Wnt2Fly/Peanut2Shield/src/hid_peripheral.cpp

#include "hid_peripheral.h"
#include "config.h"
#include "devlog.h"
#include <NimBLEDevice.h>
#include <Preferences.h>
#include <Arduino.h>
#if CFG_SHIELD_DEBUG
#include <esp_system.h>
#endif

static Preferences sShieldPrefs;

#if CFG_SHIELD_DEBUG
static unsigned long sShieldConnectAt       = 0;
static unsigned long sShieldFastParamsAt    = 0;
static unsigned long sShieldLastHeartbeatAt = 0;
static unsigned long sShieldLastDropAt      = 0;
static uint16_t      sShieldLastConnItvl    = 0;
static uint16_t      sShieldLastSupervision = 0;
#endif

static bool isTivoBondAddr(const NimBLEAddress& addr, NimBLEAddress tivoAddr, bool hasTivo) {
  if (!hasTivo) return false;
  return addr == tivoAddr;
}

// HID Report Descriptor
//   Report ID 1 — standard keyboard  (8 bytes: modifier, reserved, key[6])
//   Report ID 2 — consumer control   (2 bytes: usage LE16)
static const uint8_t kReportDesc[] = {
  // ---- Keyboard (Report ID 1) ----
  0x05, 0x01,         // Usage Page (Generic Desktop)
  0x09, 0x06,         // Usage (Keyboard)
  0xA1, 0x01,         // Collection (Application)
    0x85, 0x01,       //   Report ID (1)
    // Modifier byte
    0x05, 0x07,       //   Usage Page (Key Codes)
    0x19, 0xE0,       //   Usage Minimum (L-Ctrl)
    0x29, 0xE7,       //   Usage Maximum (R-GUI)
    0x15, 0x00,       //   Logical Minimum (0)
    0x25, 0x01,       //   Logical Maximum (1)
    0x75, 0x01,       //   Report Size (1 bit)
    0x95, 0x08,       //   Report Count (8)
    0x81, 0x02,       //   Input (Data, Variable, Absolute)
    // Reserved byte
    0x75, 0x08,       //   Report Size (8 bits)
    0x95, 0x01,       //   Report Count (1)
    0x81, 0x01,       //   Input (Constant)
    // Key array
    0x75, 0x08,       //   Report Size (8 bits)
    0x95, 0x06,       //   Report Count (6)
    0x15, 0x00,       //   Logical Minimum (0)
    0x26, 0xFF, 0x00, //   Logical Maximum (255)
    0x19, 0x00,       //   Usage Minimum (0)
    0x29, 0xFF,       //   Usage Maximum (255)
    0x81, 0x00,       //   Input (Data, Array)
  0xC0,               // End Collection

  // ---- Consumer Control (Report ID 2) ----
  0x05, 0x0C,         // Usage Page (Consumer)
  0x09, 0x01,         // Usage (Consumer Control)
  0xA1, 0x01,         // Collection (Application)
    0x85, 0x02,       //   Report ID (2)
    0x19, 0x00,       //   Usage Minimum (0)
    0x2A, 0xFF, 0x03, //   Usage Maximum (1023)
    0x15, 0x00,       //   Logical Minimum (0)
    0x26, 0xFF, 0x03, //   Logical Maximum (1023)
    0x75, 0x10,       //   Report Size (16 bits)
    0x95, 0x01,       //   Report Count (1)
    0x81, 0x00,       //   Input (Data, Array)
  0xC0,               // End Collection
};

static NimBLEServer*         pServer              = nullptr;
static NimBLECharacteristic* pKbReport            = nullptr;
static NimBLECharacteristic* pCsReport            = nullptr;
static bool                  sShieldConn          = false;
static NimBLEAddress         sShieldAddr;
static bool                  sHasShieldAddr       = false;
static uint16_t              sShieldConnHandle    = BLE_HS_CONN_HANDLE_NONE;
// true between onConnect and the first CCCD write — Shield is doing service discovery
static bool                  sShieldNegotiating   = false;
static bool                  sAdvPausedForTivo      = false;
static bool                  sTivoLinkActive        = false;
static bool                  sAdvSlowForTivo        = false;

#if CFG_SHIELD_DEBUG
static void shieldDebugLogAdv(const char* tag);
static void shieldDebugLogConnDesc(const char* tag, ble_gap_conn_desc* desc);
#endif

// Start (or restart) advertising with intervals appropriate for dual-role state.
static void startAdvertisingAppropriate() {
  NimBLEAdvertising* pAdv = NimBLEDevice::getAdvertising();
  if (!pAdv) return;

  const bool slow = sTivoLinkActive && !sShieldConn;
  if (pAdv->isAdvertising()) pAdv->stop();
  if (slow) {
    pAdv->setMinInterval(CFG_ADV_SLOW_MIN_INTERVAL);
    pAdv->setMaxInterval(CFG_ADV_SLOW_MAX_INTERVAL);
  } else {
    pAdv->setMinInterval(CFG_ADV_MIN_INTERVAL);
    pAdv->setMaxInterval(CFG_ADV_MAX_INTERVAL);
  }
  pAdv->start();
  sAdvPausedForTivo = false;
  sAdvSlowForTivo   = slow;
  if (slow) {
    DEV_LOGLN("[HID] Advertising (slow) — protecting TiVo central link.");
  } else {
    DEV_LOGLN("[HID] Advertising (fast).");
  }
}

// Log every CCCD write so we can confirm the Shield is enabling notifications
class ReportCallbacks : public NimBLECharacteristicCallbacks {
  void onSubscribe(NimBLECharacteristic* pChar,
                   ble_gap_conn_desc*    desc,
                   uint16_t             subValue) override {
    DEV_LOGF("[HID] CCCD write — subValue=0x%04X "
                  "(1=notify enabled, 0=disabled)\r\n", subValue);
    // First CCCD write means Android has finished service discovery
    if (subValue & 0x0001) {
      if (sShieldNegotiating) {
        sShieldNegotiating = false;
        hidPersistShieldBond();
      }
    }
  }
};
static ReportCallbacks sReportCbs;

class PeriphCallbacks : public NimBLEServerCallbacks {
  void onConnect(NimBLEServer* s, ble_gap_conn_desc* desc) override {
    sShieldConn         = true;
    sShieldNegotiating  = true;   // waiting for Android to write CCCDs
    sShieldAddr         = NimBLEAddress(desc->peer_id_addr);
    sHasShieldAddr      = true;
    sShieldConnHandle   = desc->conn_handle;
#if CFG_SHIELD_DEBUG
    sShieldConnectAt = millis();
#endif
    DEV_LOGF("[HID] Shield connected: %s handle=%u\r\n",
                  sShieldAddr.toString().c_str(), sShieldConnHandle);
#if CFG_SHIELD_DEBUG
    shieldDebugLogConnDesc("Shield connect", desc);
#endif
    NimBLEDevice::getAdvertising()->stop();
  }

  void onDisconnect(NimBLEServer* s, ble_gap_conn_desc* desc) override {
    unsigned long upMs = 0;
#if CFG_SHIELD_DEBUG
    if (sShieldConnectAt) upMs = millis() - sShieldConnectAt;
    unsigned long sinceFast = sShieldFastParamsAt ? (millis() - sShieldFastParamsAt) : 0;
    DEV_LOGF("[HID] Shield disconnected (up %lu ms", upMs);
    if (sShieldFastParamsAt)
      DEV_LOGF(", fast-params %lu ms ago", sinceFast);
    DEV_LOGF(")\r\n");
    shieldDebugLogConnDesc("Shield disconnect", desc);
    shieldDebugLogAdv("before re-adv");
    sShieldLastDropAt = millis();
    sShieldConnectAt  = 0;
#else
    DEV_LOGLN("[HID] Shield disconnected — re-advertising.");
#endif
    sShieldConn        = false;
    sShieldNegotiating = false;
    sShieldConnHandle  = BLE_HS_CONN_HANDLE_NONE;
    // Prefer slow advertising if TiVo is still linked — fast 20–40 ms re-adv
    // after Shield power-off often drops the TiVo central connection.
    startAdvertisingAppropriate();
#if CFG_SHIELD_DEBUG
    shieldDebugLogAdv("after re-adv");
#endif
  }

  void onMTUChange(uint16_t MTU, ble_gap_conn_desc* desc) override {
#if CFG_SHIELD_DEBUG
    DEV_LOGF("[HID-DBG] Shield MTU=%u handle=%u\r\n", MTU,
                  desc ? desc->conn_handle : 0);
#endif
  }
};

void hidPeripheralInit() {
  pServer = NimBLEDevice::createServer();
  pServer->setCallbacks(new PeriphCallbacks());

  // ---- HID Service 0x1812 ----
  NimBLEService* pHid = pServer->createService("1812");

  // Protocol Mode — boot(0) / report(1); we stay in report mode
  NimBLECharacteristic* pProto = pHid->createCharacteristic(
      "2A4E", NIMBLE_PROPERTY::READ | NIMBLE_PROPERTY::WRITE_NR);
  uint8_t proto = 0x01;
  pProto->setValue(&proto, 1);

  // Report Map
  NimBLECharacteristic* pMap = pHid->createCharacteristic(
      "2A4B", NIMBLE_PROPERTY::READ);
  pMap->setValue(kReportDesc, sizeof(kReportDesc));

  // HID Information  [bcdHID=1.11, country=0, flags=NormallyConnectable]
  NimBLECharacteristic* pInfo = pHid->createCharacteristic(
      "2A4A", NIMBLE_PROPERTY::READ);
  uint8_t hidInfo[] = {0x11, 0x01, 0x00, 0x02};
  pInfo->setValue(hidInfo, sizeof(hidInfo));

  // HID Control Point
  NimBLECharacteristic* pCtrl = pHid->createCharacteristic(
      "2A4C", NIMBLE_PROPERTY::WRITE_NR);
  uint8_t ctrlVal = 0;
  pCtrl->setValue(&ctrlVal, 1);

  // Keyboard Input Report — Report ID 1, type Input (0x01)
  pKbReport = pHid->createCharacteristic(
      "2A4D", NIMBLE_PROPERTY::READ | NIMBLE_PROPERTY::NOTIFY);
  pKbReport->setCallbacks(&sReportCbs);
  {
    NimBLEDescriptor* d = pKbReport->createDescriptor(
        "2908", NIMBLE_PROPERTY::READ, 2);
    uint8_t ref[] = {0x01, 0x01};
    d->setValue(ref, sizeof(ref));
  }
  {
    uint8_t zeros[8] = {};
    pKbReport->setValue(zeros, sizeof(zeros));
  }

  // Consumer Input Report — Report ID 2, type Input (0x01)
  pCsReport = pHid->createCharacteristic(
      "2A4D", NIMBLE_PROPERTY::READ | NIMBLE_PROPERTY::NOTIFY);
  pCsReport->setCallbacks(&sReportCbs);
  {
    NimBLEDescriptor* d = pCsReport->createDescriptor(
        "2908", NIMBLE_PROPERTY::READ, 2);
    uint8_t ref[] = {0x02, 0x01};
    d->setValue(ref, sizeof(ref));
  }
  {
    uint8_t zeros[2] = {};
    pCsReport->setValue(zeros, sizeof(zeros));
  }

  pHid->start();

  // ---- Battery Service 0x180F ----
  NimBLEService* pBatt = pServer->createService("180F");
  NimBLECharacteristic* pBattLvl = pBatt->createCharacteristic(
      "2A19", NIMBLE_PROPERTY::READ | NIMBLE_PROPERTY::NOTIFY);
  uint8_t batt = 100;
  pBattLvl->setValue(&batt, 1);
  pBatt->start();

  // ---- Device Information Service 0x180A ----
  NimBLEService* pDev = pServer->createService("180A");
  NimBLECharacteristic* pPnp = pDev->createCharacteristic(
      "2A50", NIMBLE_PROPERTY::READ);
  // vendor_id_source=BT(1), vendor=0xFFFF, product=0x0001, version=0x0001
  uint8_t pnp[] = {0x01, 0xFF, 0xFF, 0x01, 0x00, 0x01, 0x00};
  pPnp->setValue(pnp, sizeof(pnp));
  pDev->start();

  // ---- Advertising ----
  NimBLEAdvertising* pAdv = NimBLEDevice::getAdvertising();
  pAdv->addServiceUUID("1812");
  pAdv->setAppearance(CFG_BLE_APPEARANCE);
  pAdv->setScanResponse(true);
  pAdv->setMinInterval(CFG_ADV_MIN_INTERVAL);
  pAdv->setMaxInterval(CFG_ADV_MAX_INTERVAL);
  pAdv->start();

  DEV_LOGF("[HID] Peripheral ready — advertising as '%s'.\r\n", CFG_BLE_DEVICE_NAME);
}

bool hidPeripheralConnected() { return sShieldConn; }

// True only after Android has written CCCDs (bonding + service discovery complete).
// WiFi must not start before this — the radio disruption disconnects the Shield.
bool hidShieldReady() { return sShieldConn && !sShieldNegotiating; }

// Returns a string token describing the current Shield connection phase.
const char* hidGetShieldState() {
  if (sShieldConn) {
    return sShieldNegotiating ? "negotiating" : "ready";
  }
  return sHasShieldAddr ? "adv_bonded" : "advertising";
}

#if CFG_SHIELD_DEBUG
static void shieldDebugLogAdv(const char* tag) {
  NimBLEAdvertising* pAdv = NimBLEDevice::getAdvertising();
  DEV_LOGF("[HID-DBG] %s: state=%s conn=%d advPausedForTivo=%d advSlow=%d "
                "tivoLink=%d isAdvertising=%d bonded=%d\r\n",
                tag, hidGetShieldState(), sShieldConn ? 1 : 0,
                sAdvPausedForTivo ? 1 : 0, sAdvSlowForTivo ? 1 : 0,
                sTivoLinkActive ? 1 : 0,
                (pAdv && pAdv->isAdvertising()) ? 1 : 0,
                sHasShieldAddr ? 1 : 0);
}

static void shieldDebugLogConnDesc(const char* tag, ble_gap_conn_desc* desc) {
  if (!desc) {
    DEV_LOGF("[HID-DBG] %s: (no conn desc)\r\n", tag);
    return;
  }
  sShieldLastConnItvl    = desc->conn_itvl;
  sShieldLastSupervision = desc->supervision_timeout;
  DEV_LOGF("[HID-DBG] %s: handle=%u itvl=%u (%.2f ms) latency=%u sup=%u (%.0f ms)\r\n",
                tag, desc->conn_handle, desc->conn_itvl,
                desc->conn_itvl * 1.25f, desc->conn_latency,
                desc->supervision_timeout, desc->supervision_timeout * 10.0f);
}

void hidShieldDebugLogBootReason() {
  esp_reset_reason_t r = esp_reset_reason();
  const char* name = "unknown";
  switch (r) {
    case ESP_RST_POWERON:   name = "power-on"; break;
    case ESP_RST_SW:        name = "software"; break;
    case ESP_RST_PANIC:     name = "panic"; break;
    case ESP_RST_INT_WDT:   name = "int_wdt"; break;
    case ESP_RST_TASK_WDT:  name = "task_wdt"; break;
    case ESP_RST_WDT:       name = "wdt"; break;
    case ESP_RST_BROWNOUT:  name = "brownout"; break;
    case ESP_RST_DEEPSLEEP: name = "deepsleep"; break;
    default: break;
  }
  DEV_LOGF("[HID-DBG] ESP reset reason: %s (%d)\r\n", name, (int)r);
}

void hidShieldDebugTick(bool tivoConnected, bool tivoReady, bool tivoCentralBusy) {
  unsigned long now = millis();
  if (sShieldLastHeartbeatAt &&
      (now - sShieldLastHeartbeatAt) < CFG_SHIELD_DEBUG_HEARTBEAT_MS) {
    return;
  }
  sShieldLastHeartbeatAt = now;

  unsigned long upMs = sShieldConnectAt ? (now - sShieldConnectAt) : 0;
  unsigned long sinceDrop = sShieldLastDropAt ? (now - sShieldLastDropAt) : 0;
  NimBLEAdvertising* pAdv = NimBLEDevice::getAdvertising();

  DEV_LOGF("[HID-DBG] heartbeat: Shield=%s up=%lu ms lastDrop=%lu ms ago "
                "itvl=%u sup=%u | TiVo conn=%d ready=%d centralBusy=%d | "
                "adv=%d paused=%d slow=%d\r\n",
                hidGetShieldState(), upMs, sinceDrop,
                sShieldLastConnItvl, sShieldLastSupervision,
                tivoConnected ? 1 : 0, tivoReady ? 1 : 0, tivoCentralBusy ? 1 : 0,
                (pAdv && pAdv->isAdvertising()) ? 1 : 0, sAdvPausedForTivo ? 1 : 0,
                sAdvSlowForTivo ? 1 : 0);
}
#endif

// Called from loop() 3 s after Shield connects to request faster BLE intervals.
// Doing this immediately in onConnect blocks Android's CCCD setup.
void hidRequestFastParams() {
  if (!sShieldConn || sShieldConnHandle == BLE_HS_CONN_HANDLE_NONE) return;
#if CFG_SHIELD_DEBUG
  sShieldFastParamsAt = millis();
  DEV_LOGF("[HID-DBG] Requesting fast conn params (7.5–15 ms, sup %u ms) handle=%u\r\n",
                (unsigned)(CFG_CONN_TIMEOUT * 10), sShieldConnHandle);
#endif
  pServer->updateConnParams(sShieldConnHandle, CFG_CONN_MIN_INTERVAL,
                            CFG_CONN_MAX_INTERVAL, CFG_CONN_LATENCY, CFG_CONN_TIMEOUT);
  DEV_LOGLN("[HID] Requested fast conn params (7.5-15 ms) from Shield.");
}

String hidGetShieldAddr() {
  if (!sHasShieldAddr) return "";
  return String(sShieldAddr.toString().c_str());
}

bool hidHasShieldBond() { return sHasShieldAddr; }

void hidPersistShieldBond() {
  if (!sHasShieldAddr) return;
  sShieldPrefs.begin(CFG_NVS_SHIELD_NS, false);
  sShieldPrefs.putString(CFG_NVS_SHIELD_ADDR, sShieldAddr.toString().c_str());
  sShieldPrefs.end();
  DEV_LOGF("[HID] Shield bond saved: %s\r\n", sShieldAddr.toString().c_str());
}

void hidLoadShieldBond(NimBLEAddress tivoAddr, bool hasTivo) {
  bool fromNvs = false;
  sShieldPrefs.begin(CFG_NVS_SHIELD_NS, true);
  String shieldStr = sShieldPrefs.getString(CFG_NVS_SHIELD_ADDR, "");
  sShieldPrefs.end();

  if (shieldStr.length() > 0) {
    sShieldAddr    = NimBLEAddress(shieldStr.c_str());
    sHasShieldAddr = true;
    fromNvs        = true;
    DEV_LOGF("[HID] Shield address from NVS: %s\r\n", shieldStr.c_str());
  }

  NimBLEAddress bleShield;
  bool foundBle = false;
  int n = NimBLEDevice::getNumBonds();
  for (int i = 0; i < n; i++) {
    NimBLEAddress addr = NimBLEDevice::getBondedAddress(i);
    if (isTivoBondAddr(addr, tivoAddr, hasTivo)) continue;
    bleShield = addr;
    foundBle  = true;
    break;
  }

  if (foundBle) {
    if (!fromNvs) {
      sShieldAddr    = bleShield;
      sHasShieldAddr = true;
      DEV_LOGF("[HID] Found stored Shield bond: %s\r\n", bleShield.toString().c_str());
      hidPersistShieldBond();
      return;
    }
    if (bleShield == sShieldAddr) {
      DEV_LOGF("[HID] NimBLE bond matches Shield NVS.\r\n");
      return;
    }
    DEV_LOGF("[HID] WARNING: NVS Shield %s != NimBLE bond %s — using NVS.\r\n",
                  sShieldAddr.toString().c_str(), bleShield.toString().c_str());
    return;
  }

  if (fromNvs) {
    DEV_LOGLN("[HID] WARNING: Shield in NVS but no NimBLE bond — re-pair from Shield.");
    return;
  }

  sHasShieldAddr = false;
  DEV_LOGLN("[HID] No stored Shield bond found.");
}

void hidSendKeyboard(uint8_t modifier, uint8_t keycode) {
  if (!pKbReport || !sShieldConn) return;
  uint8_t r[8] = {modifier, 0x00, keycode, 0, 0, 0, 0, 0};
  pKbReport->setValue(r, sizeof(r));
  pKbReport->notify();
  DEV_LOGF("[HID] KB notify mod=0x%02X key=0x%02X\r\n", modifier, keycode);
}

void hidReleaseKeyboard() {
  if (!pKbReport) return;
  uint8_t r[8] = {};
  pKbReport->setValue(r, sizeof(r));
  if (sShieldConn) pKbReport->notify();
}

void hidSendKeyboardRaw(const uint8_t* report8) {
  if (!pKbReport || !sShieldConn) return;
  pKbReport->setValue(report8, 8);
  pKbReport->notify();
}

void hidSendConsumer(uint16_t usage) {
  if (!pCsReport || !sShieldConn) return;
  uint8_t r[2] = {(uint8_t)(usage & 0xFF), (uint8_t)(usage >> 8)};
  pCsReport->setValue(r, sizeof(r));
  pCsReport->notify();
  DEV_LOGF("[HID] CSM notify 0x%04X\r\n", usage);
}

void hidReleaseConsumer() {
  if (!pCsReport) return;
  uint8_t r[2] = {};
  pCsReport->setValue(r, sizeof(r));
  if (sShieldConn) pCsReport->notify();
}

void hidPauseForTivoCentral() {
  // Shield not linked: never go dark — Android cannot reconnect if we stop advertising.
  // Use slow intervals so dual-role TiVo connect still gets radio time.
  if (!sShieldConn) {
    if (!sAdvPausedForTivo) {
      DEV_LOGLN("[HID] TiVo connecting — keeping advertising (slow) for Shield.");
#if CFG_SHIELD_DEBUG
      DEV_LOGF("[HID-DBG] no-pause for TiVo (Shield conn=0 state=%s)\r\n",
                    hidGetShieldState());
#endif
    }
    sTivoLinkActive = true;
    startAdvertisingAppropriate();
    return;
  }

  if (sAdvPausedForTivo) return;
  NimBLEAdvertising* pAdv = NimBLEDevice::getAdvertising();
  if (pAdv && pAdv->isAdvertising()) {
    pAdv->stop();
    DEV_LOGLN("[HID] Advertising paused for TiVo central.");
#if CFG_SHIELD_DEBUG
    DEV_LOGF("[HID-DBG] pause for TiVo (Shield conn=%d state=%s)\r\n",
                  sShieldConn ? 1 : 0, hidGetShieldState());
#endif
  }
  sAdvPausedForTivo = true;
  sAdvSlowForTivo   = false;
}

void hidResumeAfterTivoCentral() {
  if (!sAdvPausedForTivo) {
    // Shield disconnect may already have started advertising; still refresh
    // intervals if TiVo link state wants slow/fast differently.
    if (!sShieldConn) {
      const bool wantSlow = sTivoLinkActive;
      if (wantSlow != sAdvSlowForTivo) startAdvertisingAppropriate();
    }
    return;
  }
  if (sShieldConn) {
    sAdvPausedForTivo = false;
    sAdvSlowForTivo   = false;
#if CFG_SHIELD_DEBUG
    shieldDebugLogAdv("TiVo central done (Shield up, no adv)");
#endif
    return;
  }
  startAdvertisingAppropriate();
#if CFG_SHIELD_DEBUG
  shieldDebugLogAdv("TiVo central done");
#endif
}

void hidSetTivoLinkActive(bool active) {
  if (sTivoLinkActive == active) return;
  sTivoLinkActive = active;
#if CFG_SHIELD_DEBUG
  DEV_LOGF("[HID-DBG] TiVo link active=%d\r\n", active ? 1 : 0);
#endif
  if (sShieldConn || sAdvPausedForTivo) return;

  NimBLEAdvertising* pAdv = NimBLEDevice::getAdvertising();
  if (!pAdv) return;

  const bool wantSlow = active;
  if (pAdv->isAdvertising()) {
    if (wantSlow != sAdvSlowForTivo) startAdvertisingAppropriate();
  } else if (!active) {
    // TiVo dropped while not advertising — restore fast discoverability.
    startAdvertisingAppropriate();
  }
}

// Rebuild and start advertising with the correct HID service data.
// Called after bond deletion or TX power change so the advertising PDU is
// always fresh — NimBLE can drop it after stack-level resets.
static void restartAdvertising();   // forward declaration for hidForgetShield
void hidRestartAdvertising() { restartAdvertising(); }

static void restartAdvertising() {
  NimBLEAdvertising* pAdv = NimBLEDevice::getAdvertising();
  pAdv->stop();
  delay(CFG_ADV_RESTART_SETTLE_MS);
  // Do NOT call addServiceUUID/setAppearance here — those are already configured
  // in hidPeripheralInit() and persist in the NimBLEAdvertising object after stop().
  // Calling addServiceUUID again would add a duplicate 0x1812 entry, producing a
  // malformed advertising PDU that Android TV silently ignores.
  startAdvertisingAppropriate();
  DEV_LOGF("[HID] Advertising restarted — isAdvertising=%d\r\n",
                pAdv->isAdvertising() ? 1 : 0);
}

void hidForgetShield(NimBLEAddress tivoAddr, bool hasTivo) {
  NimBLEAdvertising* pAdv = NimBLEDevice::getAdvertising();
  pAdv->stop();

  // Disconnect the Shield using its known address (avoids wrong-handle bug)
  if (sShieldConn && pServer && sHasShieldAddr) {
    NimBLEConnInfo info = pServer->getPeerInfo(sShieldAddr);
    uint16_t handle = info.getConnHandle();
    if (handle != BLE_HS_CONN_HANDLE_NONE) {
      pServer->disconnect(handle);
      DEV_LOGF("[HID] Disconnecting Shield handle %u\r\n", handle);
    }
    sShieldConn        = false;
    sShieldNegotiating = false;
    sShieldConnHandle  = BLE_HS_CONN_HANDLE_NONE;
  }

  // Delete all BLE bonds except the TiVo remote's bond
  int n = NimBLEDevice::getNumBonds();
  int deleted = 0;
  for (int i = n - 1; i >= 0; i--) {
    NimBLEAddress addr = NimBLEDevice::getBondedAddress(i);
    if (hasTivo && addr == tivoAddr) continue;
    NimBLEDevice::deleteBond(addr);
    DEV_LOGF("[HID] Deleted bond: %s\r\n", addr.toString().c_str());
    deleted++;
  }
  sHasShieldAddr = false;
  sShieldPrefs.begin(CFG_NVS_SHIELD_NS, false);
  if (sShieldPrefs.isKey(CFG_NVS_SHIELD_ADDR))
    sShieldPrefs.remove(CFG_NVS_SHIELD_ADDR);
  sShieldPrefs.end();
  DEV_LOGF("[HID] Shield bond cleared (%d removed).\r\n", deleted);

  delay(CFG_BOND_DELETE_SETTLE_MS);
  restartAdvertising();
  DEV_LOGLN("[HID] Ready — pair from Shield now.");
}
