Wnt2Fly/Peanut2Shield/src/keymap.cpp

#include "keymap.h"
#include "config.h"
#include "devlog.h"
#include <Preferences.h>
#include <string.h>

static Preferences sPrefs;

// Built-in default translations — entries defined in config.h via CFG_DEFAULT_KEYMAP
#define _KM_ROW(src, type, dst)  { src, OutputType::type, dst },
static const RemapEntry kDefaults[] = { CFG_DEFAULT_KEYMAP(_KM_ROW) };
#undef _KM_ROW

static RemapEntry sCustom[KEYMAP_MAX_CUSTOM];
static int        sCustomCount = 0;

void keymapInit() {
  sPrefs.begin(CFG_NVS_KEYMAP_NS, false);
  sCustomCount = (int)sPrefs.getInt(CFG_NVS_KEYMAP_CNT, 0);
  if (sCustomCount < 0 || sCustomCount > KEYMAP_MAX_CUSTOM)
    sCustomCount = 0;
  for (int i = 0; i < sCustomCount; i++) {
    char key[8];
    snprintf(key, sizeof(key), CFG_NVS_KEYMAP_ROW "%d", i);
    sPrefs.getBytes(key, &sCustom[i], sizeof(RemapEntry));
  }
  DEV_LOGF("[Keymap] Loaded %d custom remap(s).\r\n", sCustomCount);
}

static void nvsSave() {
  sPrefs.putInt(CFG_NVS_KEYMAP_CNT, sCustomCount);
  for (int i = 0; i < sCustomCount; i++) {
    char key[8];
    snprintf(key, sizeof(key), CFG_NVS_KEYMAP_ROW "%d", i);
    sPrefs.putBytes(key, &sCustom[i], sizeof(RemapEntry));
  }
}

bool keymapLookupConsumer(uint16_t srcCode, OutputType& outType, uint16_t& outCode) {
  // Custom overrides checked first
  for (int i = 0; i < sCustomCount; i++) {
    if (sCustom[i].srcCode == srcCode) {
      outType = sCustom[i].outputType;
      outCode = sCustom[i].dstCode;
      return true;
    }
  }
  // Built-in defaults
  for (const auto& e : kDefaults) {
    if (e.srcCode == srcCode) {
      outType = e.outputType;
      outCode = e.dstCode;
      return true;
    }
  }
  // Passthrough as consumer
  outType = OutputType::Consumer;
  outCode = srcCode;
  return false;
}

bool keymapAdd(uint16_t srcCode, OutputType outType, uint16_t dstCode) {
  for (int i = 0; i < sCustomCount; i++) {
    if (sCustom[i].srcCode == srcCode) {
      sCustom[i].outputType = outType;
      sCustom[i].dstCode    = dstCode;
      nvsSave();
      return true;
    }
  }
  if (sCustomCount >= KEYMAP_MAX_CUSTOM) return false;
  sCustom[sCustomCount++] = {srcCode, outType, dstCode};
  nvsSave();
  return true;
}

bool keymapRemove(uint16_t srcCode) {
  for (int i = 0; i < sCustomCount; i++) {
    if (sCustom[i].srcCode == srcCode) {
      memmove(&sCustom[i], &sCustom[i + 1],
              (sCustomCount - i - 1) * sizeof(RemapEntry));
      sCustomCount--;
      nvsSave();
      return true;
    }
  }
  return false;
}

void keymapClearCustom() {
  sCustomCount = 0;
  sPrefs.clear();
  sPrefs.putInt(CFG_NVS_KEYMAP_CNT, 0);
}

int keymapGetCustom(RemapEntry* buf, int maxCount) {
  int n = (sCustomCount < maxCount) ? sCustomCount : maxCount;
  memcpy(buf, sCustom, n * sizeof(RemapEntry));
  return n;
}

int keymapGetDefaultCount() {
  return (int)(sizeof(kDefaults) / sizeof(kDefaults[0]));
}

const RemapEntry* keymapGetDefaultAt(int i) {
  int n = (int)(sizeof(kDefaults) / sizeof(kDefaults[0]));
  if (i < 0 || i >= n) return nullptr;
  return &kDefaults[i];
}
